trietngh/projet_xenomai/doc/sujets/tex/conception/figures_pdf/trad_AADL.pdf

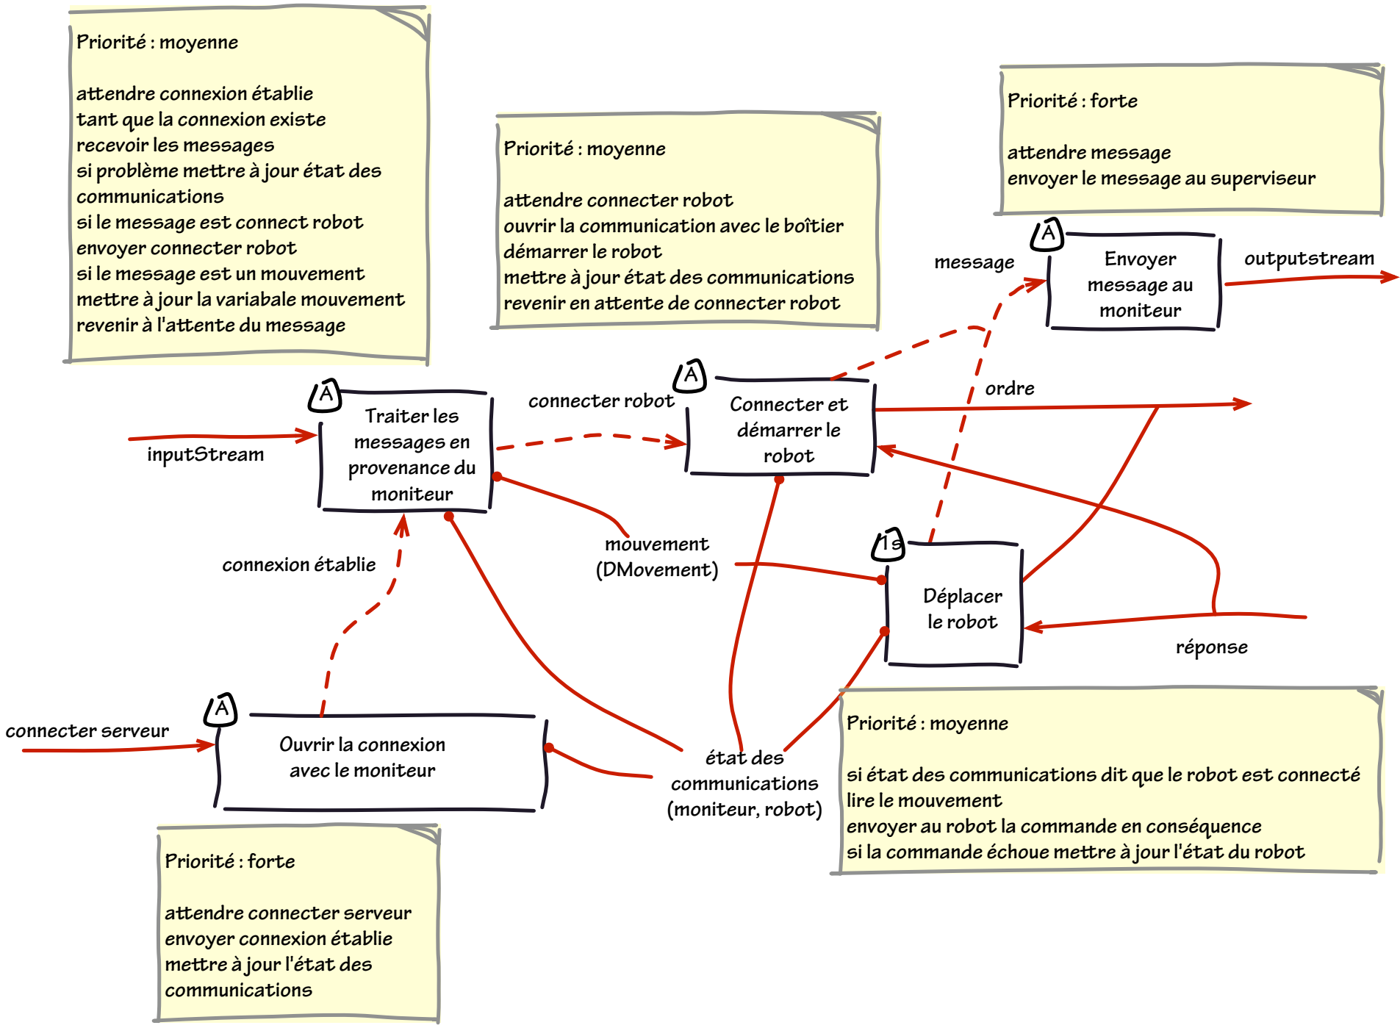
[picture p1: figure]
Traiter les messages en provenance du moniteur; inputStream; Connecter et démarrer le robot; connecter robot; ordre; Déplacer le robot; réponse; Ouvrir la connexion avec le moniteur; connecter serveur; mouvement (DMovement); état des communications (moniteur, robot); connexion établie; Priorité : forte; aendre connecter serveur envoyer connexion établie mere à jour l'état des communications; Priorité : moyenne; lire le mouvement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

si état des communications dit que le robot est connecté

envoyer au robot la commande en conséquence
si la commande échoue mere à jour l'état du robot
