trietngh/projet_xenomai/doc/sujets/tex/conception/figures_pdf/fonc/fonc10.pdf

ouvrir socket
Etablissement de la connexion avec le moniteur
start | démarrer serveur

serveur démarré

Fonction : démarrer serveur

lancer serveur
si échec afficher un message et stopper le programme sinon produire ‘serveur démarré’

Fonction : connecter au moniteur

attendre ‘serveur démarré’
appeler AcceptClient et attendre ‘ouvrir socket’ si ok produire ‘connexion établie’

Traiter les
messages en
provenance du
moniteur

inputStream

Fonction : traiter les message en provenance du moniteur

attendre ‘connexion établie’
tant que
attendre message de inputStream /*Read*/
// traiter le message
si message est ‘ouvrir communication robot’ produire ‘ouvrir comRobot’
sinon si message est ‘démarrer robot sans wd’ produit ‘démarrer robot sans wd ‘
finsi
fin tant que

connexion établie

Envoyer
message au
moniteur

outputstream

Fonction : envoyer message au moniteur

attendre ‘connexion établie’
tant que
attendre messageToMon
envoyer le message au superviseur /*Write*/ fin tant que

messageToMon

Mettre en place la
communication avec
ouvrir comRobot | le robot

Fonction : Mettre en place la communication avec le robot

attendre ‘ouvrir comRobot’
mettre en place la communication avec le robot
si la communication est ok
poster messageToMon ACK
sinon
poster messageToMon NAC
fin tant que

Démarrer
robot sans wd

ordre

réponse

démarrer robot sans wd

Fonction : démarrer robot sans wd

attendre ‘démarrer robot sans wd’
envoyer ordre de démarrer sans wd au robot si l’ordre est ok
poster messageToMon ACK
sinon
poster messageToMon NAC
