trietngh/projet_xenomai/doc/sujets/tex/conception/figures_pdf/fonc/fonc7.pdf

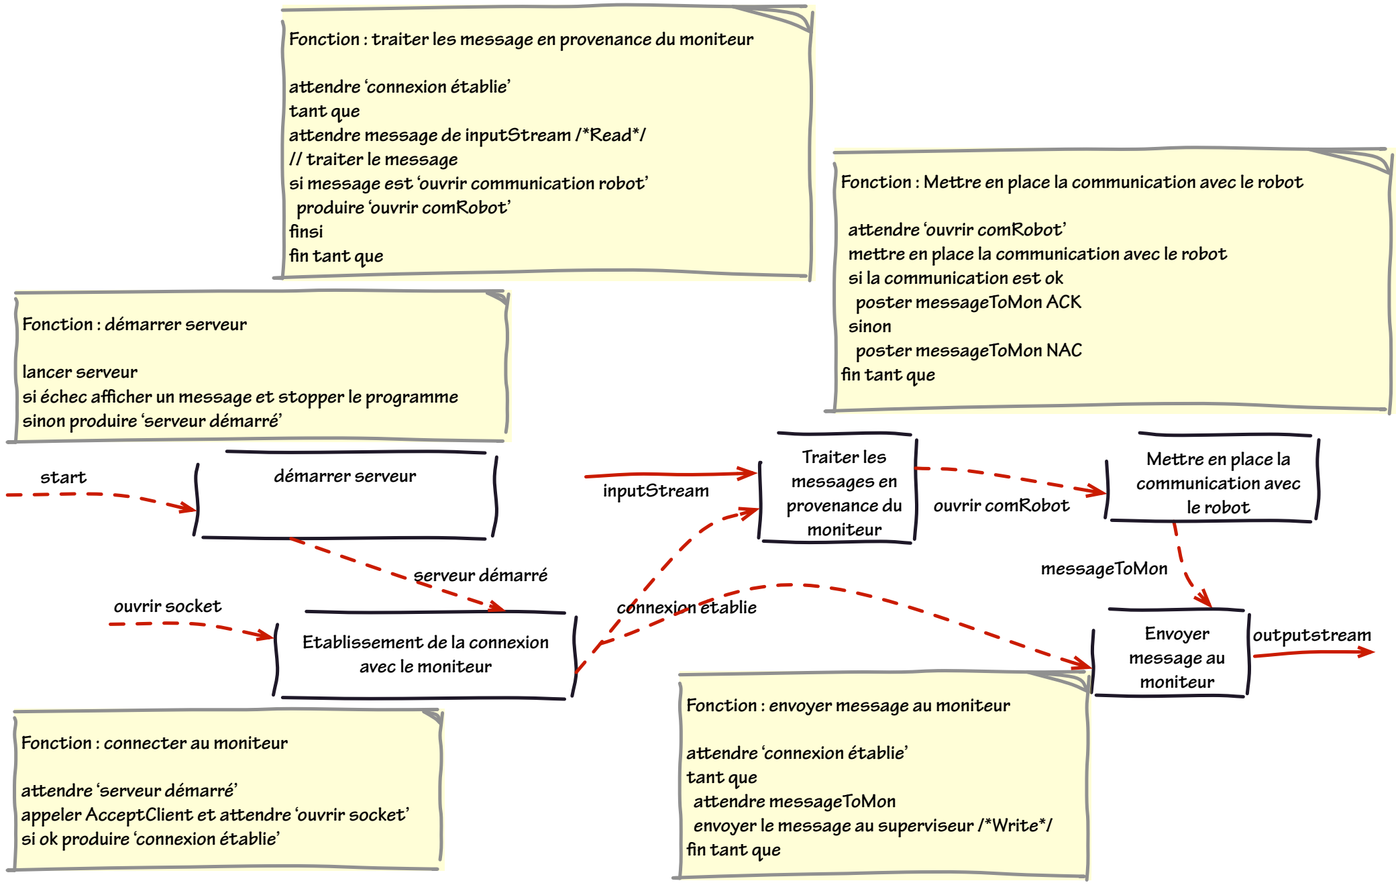
[picture p2: figure]
ouvrir socket; Etablissement de la connexion avec le moniteur; start; démarrer serveur; serveur démarré; Fonction : démarrer serveur; lancer serveur; sinon produire ‘serveur démarré’; Fonction : connecter au moniteur; attendre ‘serveur démarré’; si ok produire ‘connexion établie’; Traiter les messages en provenance du moniteur; inputStream; attendre ‘connexion établie’ tant que attendre message de inputStream /*Read*/ // traiter le message; produire ‘ouvrir comRobot’ finsi fin tant que; connexion établie; Envoyer message au moniteur; outputstream; Fonction : envoyer message au moniteur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

si échec afficher un message et stopper le programme

appeler AcceptClient et attendre ‘ouvrir socket’

Fonction : traiter les message en provenance du moniteur

si message est ‘ouvrir communication robot’

envoyer le message au superviseur /*Write*/

Fonction : Mettre en place la communication avec le robot

mettre en place la communication avec le robot
