trietngh/projet_xenomai/doc/sujets/tex/conception/figures_pdf/activity/th_openComRobot.png

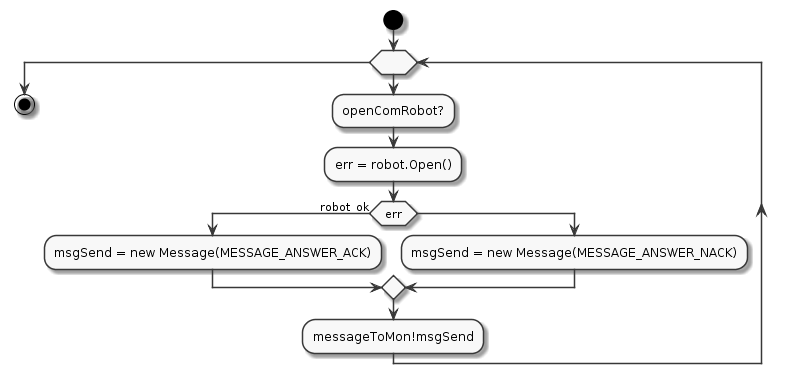
doc/sujets/tex/conception/figures_pdf/activity/th_openComRobot.png
