trietngh/projet_xenomai/doc/sujets/tex/conception/figures_pdf/activity/th_startRobot.png

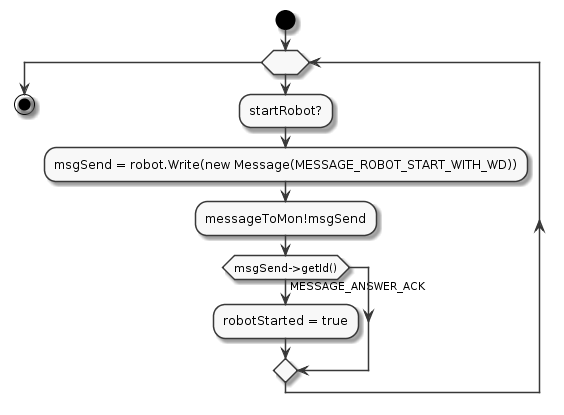
doc/sujets/tex/conception/figures_pdf/activity/th_startRobot.png
