trietngh/projet_xenomai/doc/sujets/tex/rapport_etudiant/figures-pdf/th_receiveFromMon.png

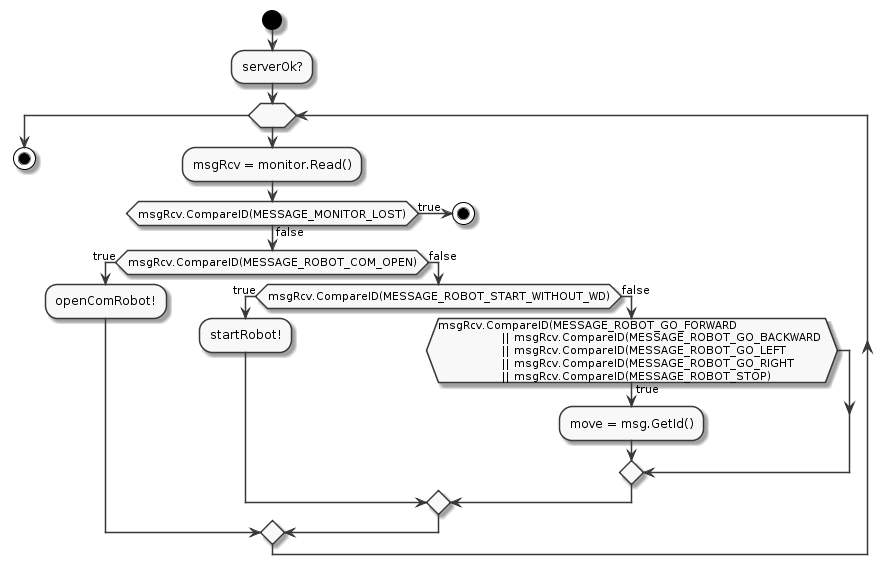
doc/sujets/tex/rapport_etudiant/figures-pdf/th_receiveFromMon.png
