trietngh/projet_xenomai/doc/sujets/tex/rapport_etudiant/figures-pdf/th_server.png

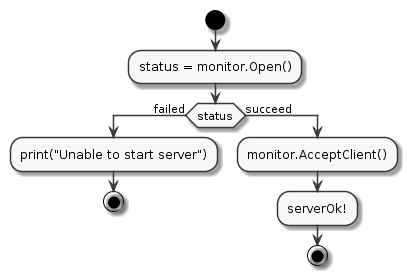
doc/sujets/tex/rapport_etudiant/figures-pdf/th_server.png
