trietngh/projet_xenomai/doc/sujets/tex/specifications/figures/schema_general2.graffle/image3.tiff

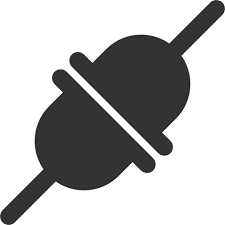
doc/sujets/tex/specifications/figures/schema_general2.graffle/image3.tiff
