trietngh/projet_xenomai/doc/sujets/tex/specifications/figures_pdf/classes1.png

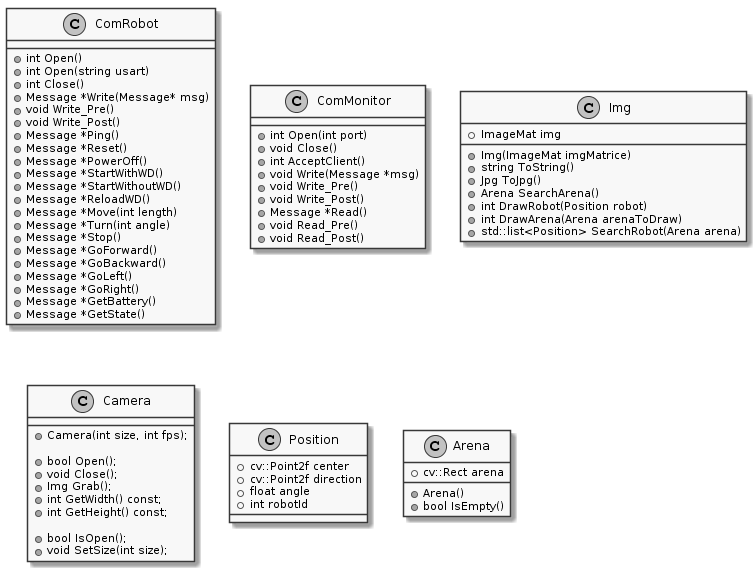
doc/sujets/tex/specifications/figures_pdf/classes1.png
