trietngh/projet_xenomai/doc/sujets/tex/specifications/figures_pdf/classes2.png

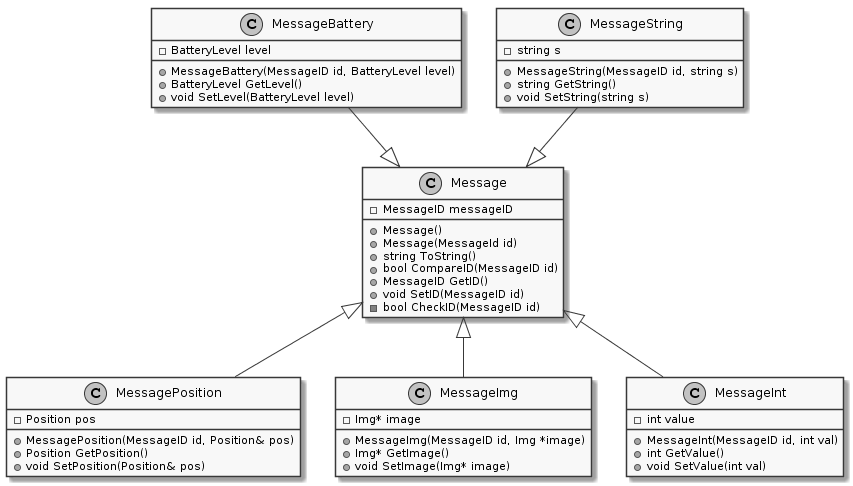
doc/sujets/tex/specifications/figures_pdf/classes2.png
