trietngh/projet_xenomai/doc/sujets/tex/specifications/seq_req/req1-2.png

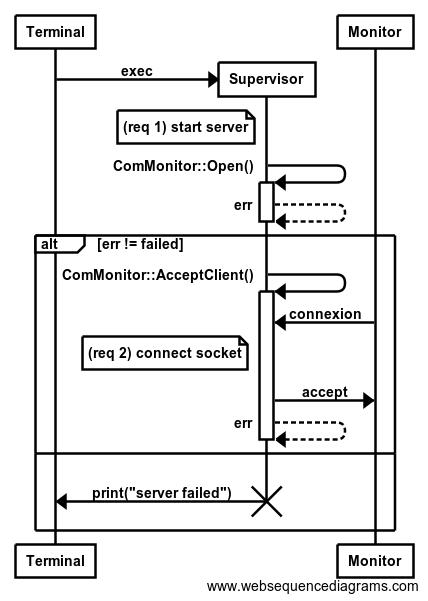
doc/sujets/tex/specifications/seq_req/req1-2.png
