trietngh/projet_xenomai/doc/sujets/tex/specifications/seq_req/req10-11.png

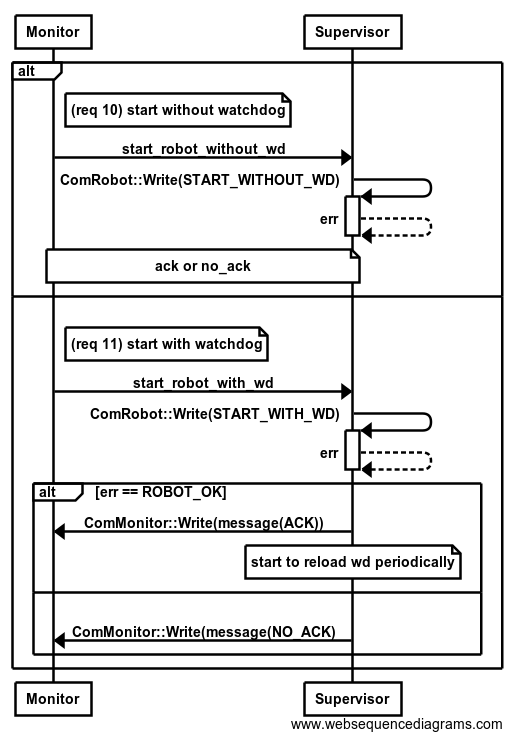
doc/sujets/tex/specifications/seq_req/req10-11.png
