trietngh/projet_xenomai/doc/sujets/tex/specifications/seq_req/req12-13.png

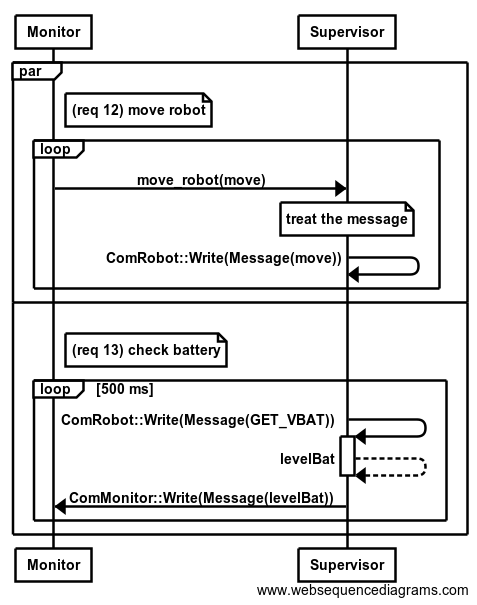
doc/sujets/tex/specifications/seq_req/req12-13.png
