trietngh/projet_xenomai/doc/sujets/tex/specifications/seq_req/req18.png

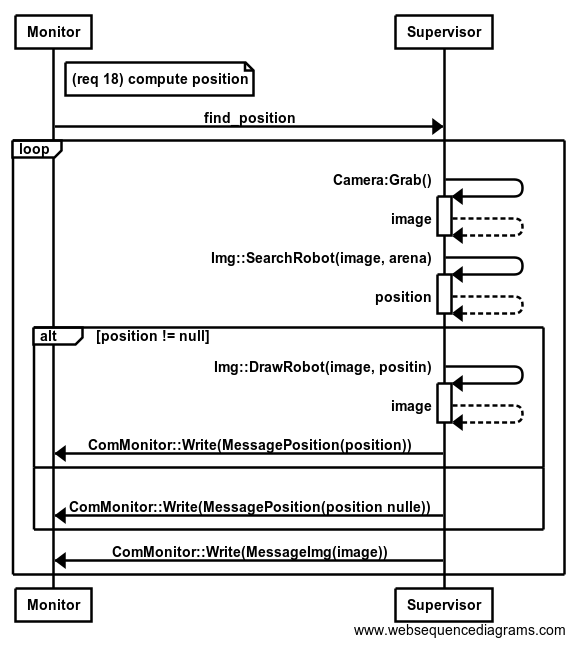
doc/sujets/tex/specifications/seq_req/req18.png
