trietngh/projet_xenomai/hardware/meca/Export/pied.stp

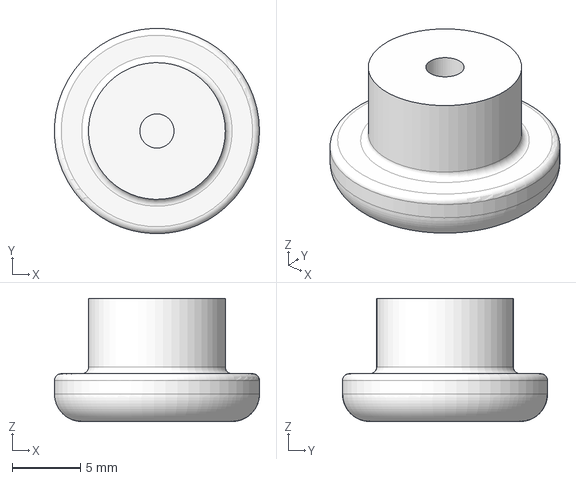
[picture p34: CAD file, 2024-04-24]
hardware/meca/Export/pied.stp
15.0 x 15.0 x 9.00 mm
