trietngh/projet_xenomai/hardware/pcb/Dumber-v3/ecran/ecran/Gerber/ecran-PTH-drl_map.dxf

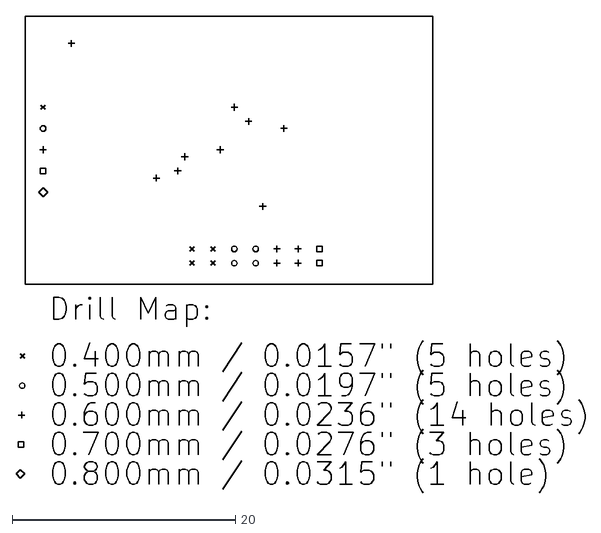
[picture p35: CAD file, 2024-04-24]
hardware/pcb/Dumber-v3/ecran/ecran/Gerber/ecran-PTH-drl_map.dxf
51.0 x 42.7
