trietngh/projet_xenomai/hardware/pcb/Models/Bloc roue.stp

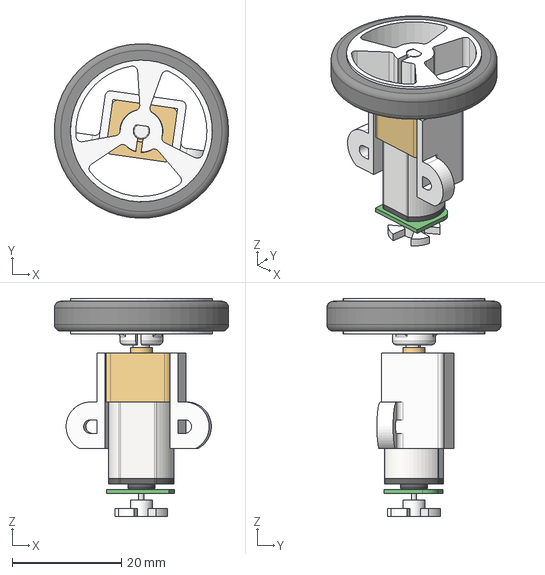
[picture p36: CAD file, 2024-04-24]
hardware/pcb/Models/Bloc roue.stp
32.0 x 32.0 x 40.0 mm
