trietngh/projet_xenomai/hardware/meca/Bibliotheque/headers/original.stl

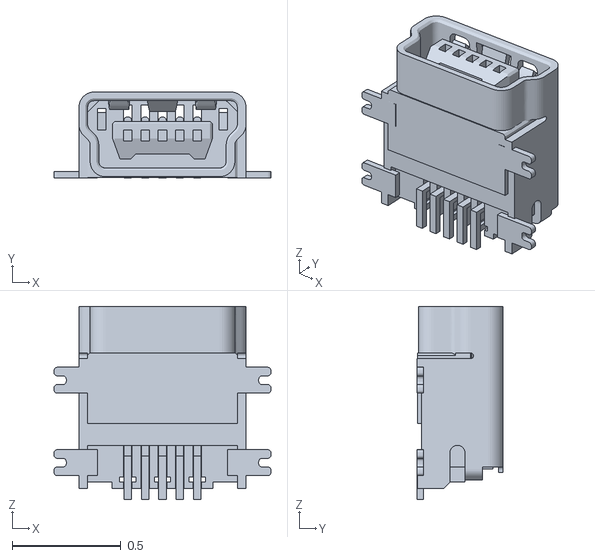
[picture p37: CAD file, 2024-04-24]
hardware/meca/Bibliotheque/headers/original.stl
1.00 x 0.396 x 0.89
