trietngh/projet_xenomai/hardware/meca/Bibliotheque/USB_Mini_B_SMD_buchse.STEP

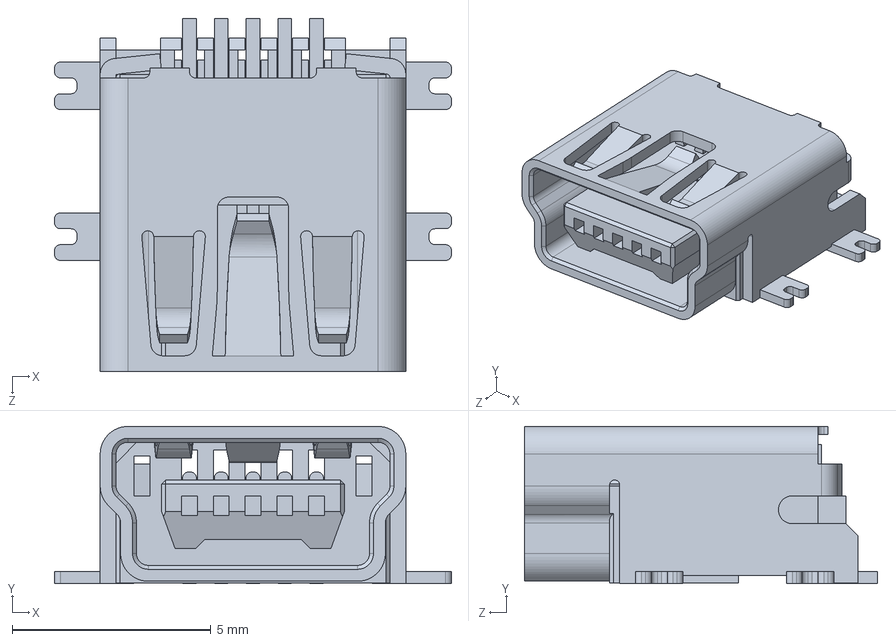
[picture p38: CAD file, 2024-04-24]
hardware/meca/Bibliotheque/USB_Mini_B_SMD_buchse.STEP
10.0 x 3.96 x 8.90 mm
