trietngh/projet_xenomai/hardware/meca/Bibliotheque/Push Button Switch.STEP

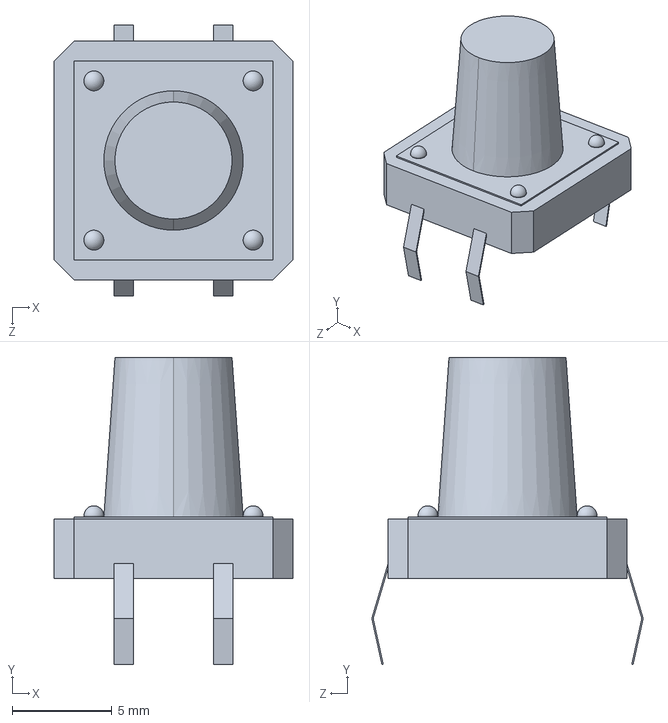
[picture p39: CAD file, 2024-04-24]
hardware/meca/Bibliotheque/Push Button Switch.STEP
12.0 x 15.4 x 13.6 mm
