trietngh/projet_xenomai/hardware/meca/Bibliotheque/0605-LED_Verde.STEP

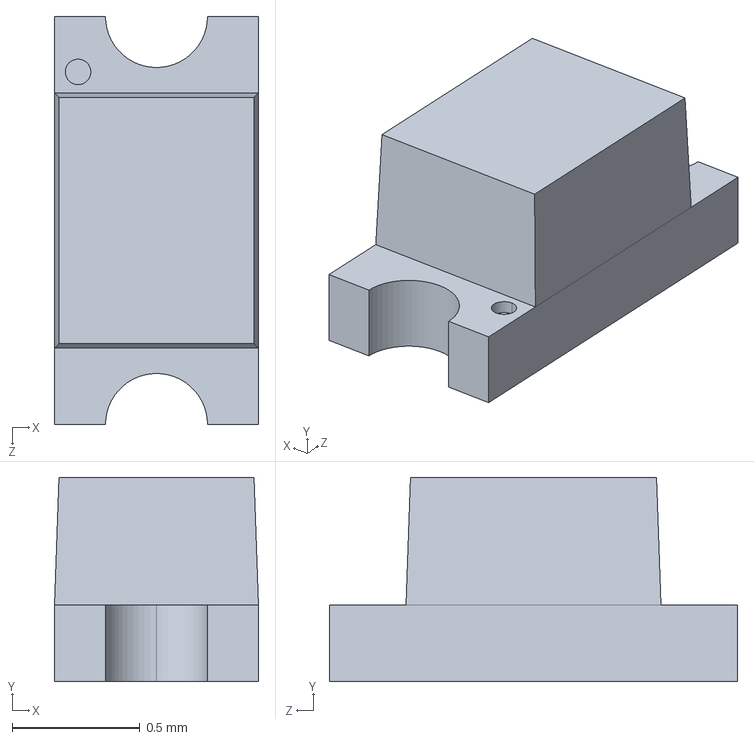
[picture p40: CAD file, 2024-04-24]
hardware/meca/Bibliotheque/0605-LED_Verde.STEP
0.8 x 0.8 x 1.60 mm
