trietngh/projet_xenomai/doc/sujets/tex/conception/figures_pdf/fonc/fonc3-4.pdf

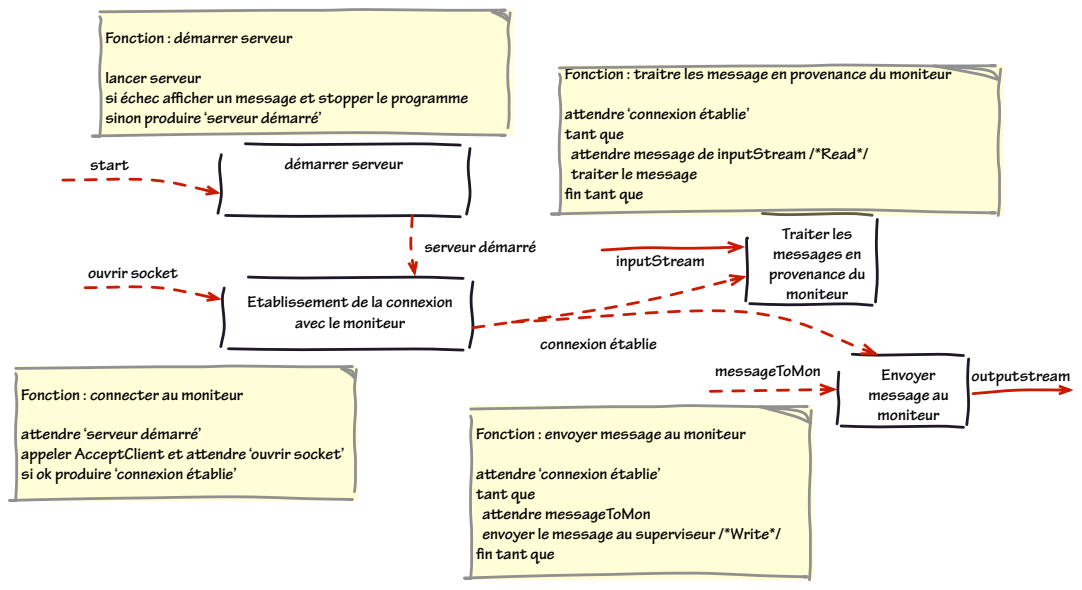
[picture p62: page 1]
ouvrir socket; start; démarrer serveur; serveur démarré; Traiter les messages en provenance du moniteur; inputStream; connexion établie; Envoyer message au moniteur; outputstream; messageToMon

Fonction : démarrer serveur

Fonction : traitre les message en provenance du moniteur

lancer serveur
si échec afficher un message et stopper le programme
sinon produire ‘serveur démarré’

attendre ‘connexion établie’
tant que
attendre message de inputStream /*Read*/
traiter le message
fin tant que

Etablissement de la connexion
avec le moniteur

Fonction : connecter au moniteur

attendre ‘serveur démarré’
appeler AcceptClient et attendre ‘ouvrir socket’
si ok produire ‘connexion établie’

Fonction : envoyer message au moniteur

attendre messageToMon
envoyer le message au superviseur /*Write*/
