trietngh/projet_xenomai/software/dumber3/Core/Inc/main.h

#define BATTERY_SENSE_Pin GPIO_PIN_0
#define BATTERY_SENSE_GPIO_Port GPIOA
#define ENC_PHA_GAUCHE_Pin GPIO_PIN_1
#define ENC_PHA_GAUCHE_GPIO_Port GPIOA
#define ENC_PHA_DROIT_Pin GPIO_PIN_2
#define ENC_PHA_DROIT_GPIO_Port GPIOA
#define ENC_PHB_GAUCHE_Pin GPIO_PIN_5
#define ENC_PHB_GAUCHE_GPIO_Port GPIOA
#define PWM_B_GAUCHE_Pin GPIO_PIN_6
#define PWM_B_GAUCHE_GPIO_Port GPIOA
#define PWM_A_GAUCHE_Pin GPIO_PIN_7
#define PWM_A_GAUCHE_GPIO_Port GPIOA
#define PWM_A_DROIT_Pin GPIO_PIN_0
#define PWM_A_DROIT_GPIO_Port GPIOB
#define PWM_B_DROIT_Pin GPIO_PIN_1
#define PWM_B_DROIT_GPIO_Port GPIOB
#define USART_TX_Pin GPIO_PIN_10
#define USART_TX_GPIO_Port GPIOB
#define USART_RX_Pin GPIO_PIN_11
#define USART_RX_GPIO_Port GPIOB
#define LED_SEG_A_Pin GPIO_PIN_12
#define LED_SEG_A_GPIO_Port GPIOB
#define LED_SEG_B_Pin GPIO_PIN_13
#define LED_SEG_B_GPIO_Port GPIOB
#define LED_SEG_C_Pin GPIO_PIN_14
#define LED_SEG_C_GPIO_Port GPIOB
#define SHUTDOWN_ENCODERS_Pin GPIO_PIN_15
#define SHUTDOWN_ENCODERS_GPIO_Port GPIOB
#define LED_SEG_D_Pin GPIO_PIN_8
#define LED_SEG_D_GPIO_Port GPIOA
#define LED_SEG_E_Pin GPIO_PIN_9
#define LED_SEG_E_GPIO_Port GPIOA
#define XBEE_RESET_Pin GPIO_PIN_10
#define XBEE_RESET_GPIO_Port GPIOA
#define LED_SEG_F_Pin GPIO_PIN_11
#define LED_SEG_F_GPIO_Port GPIOA
#define LED_SEG_G_Pin GPIO_PIN_12
#define LED_SEG_G_GPIO_Port GPIOA
#define LED_SEG_DP_Pin GPIO_PIN_15
#define LED_SEG_DP_GPIO_Port GPIOA
#define BUTTON_SENSE_Pin GPIO_PIN_3
#define BUTTON_SENSE_GPIO_Port GPIOB
#define BUTTON_SENSE_EXTI_IRQn EXTI2_3_IRQn
#define USB_SENSE_Pin GPIO_PIN_4
#define USB_SENSE_GPIO_Port GPIOB
#define USB_SENSE_EXTI_IRQn EXTI4_15_IRQn
#define CHARGER_ST2_Pin GPIO_PIN_6
#define CHARGER_ST2_GPIO_Port GPIOB
#define CHARGER_ST1_Pin GPIO_PIN_7
#define CHARGER_ST1_GPIO_Port GPIOB
#define SHUTDOWN_5V_Pin GPIO_PIN_8
#define SHUTDOWN_5V_GPIO_Port GPIOB
#define SHUTDOWN_Pin GPIO_PIN_9
#define SHUTDOWN_GPIO_Port GPIOB
