trietngh/projet_xenomai/software/raspberry/superviseur-robot-dumber-pthread/main.cpp

/*
 * Copyright (C) 2018 dimercur
 *
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
 * You should have received a copy of the GNU General Public License
 * along with this program.  If not, see <http://www.gnu.org/licenses/>.
 */

#include <iostream>
#include <unistd.h>

#include <sys/mman.h>

#ifdef __WITH_PTHREAD__
#include "tasks_pthread.h"
#else
#include "tasks.h"
#endif // __WITH_PTHREAD__

int main(int argc, char **argv) {
    Tasks tasks;
    
    
    //Lock the memory to avoid memory swapping for this program
    mlockall(MCL_CURRENT | MCL_FUTURE);

    cout<<"#################################"<<endl;
    cout<<"#      DE STIJL PROJECT         #"<<endl;
    cout<<"#################################"<<endl;

    tasks.Init();
    
    if (tasks.AcceptClient()) {
        cout << "Rock'n'Roll baby, client accepted!"<<endl<<flush;
        tasks.Run();
        
        tasks.Join();
    }
    
    tasks.Stop();
    
    //tasks.Run();

    return 0;
}
